kien242/MrReflow/src/Config.h

/**
 *  Copyright (C) 2018  foxis (Andrius Mikonis <andrius.mikonis@gmail.com>)
 *
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
 *  You should have received a copy of the GNU General Public License
 *  along with this program.  If not, see <http://www.gnu.org/licenses/>.
 **/

#ifndef CONFIG_H
#define CONFIG_H

#include <FS.h> //this needs to be first, or it all crashes and burns...
#include "SPIFFS.h"
#include <ArduinoJson.h>
#include <ESPAsyncWebServer.h>
#include <map>
#include "wificonfig.h"

#define RELAY 25

#define I2C_SDA 21
#define I2C_SCL 22



class Config
{
public:
  typedef struct
  {
    float P, I, D;
  } PID_t;

  class Stage
  {
  public:
    Stage(const char *n, const char *p, float t, float r, float s);

    String name;
    String pid;
    float target;
    float rate;
    float stay;
  };
  typedef std::vector<Stage>::iterator stages_iterator;

  class Profile
  {
  public:
    Profile(JsonObject &json);

    stages_iterator begin() { return stages.begin(); }
    stages_iterator end() { return stages.end(); }

    std::vector<Stage> stages;
    String name;
  };

  typedef std::map<String, Profile>::iterator profiles_iterator;

public:
  String cfgName;
  String profilesName;
  std::map<String, String> networks;

  std::map<String, PID_t> pid;
  std::map<String, Profile> profiles;

public:
  String hostname;
  String user;
  String password;
  String otaPassword;
  float measureInterval;
  float reportInterval;
  int tuner_id;
  double tuner_init_output;
  double tuner_noise_band;
  double tuner_output_step;

  typedef std::function<bool(JsonObject &json, Config *self)> THandlerFunction_parse;

public:
  Config(const String &cfg, const String &profiles);

  bool load_config();

  bool load_profiles();

  bool load_json(const String &name, size_t max_size, THandlerFunction_parse parser);

  bool save_config(AsyncWebServerRequest *request, uint8_t *data, size_t len, size_t index, size_t total);
  bool save_profiles(AsyncWebServerRequest *request, uint8_t *data, size_t len, size_t index, size_t total);

  bool save_file(AsyncWebServerRequest *request, const String &fname, uint8_t *data, size_t len, size_t index, size_t total);
};

void S_printf(const char *format, ...);

#endif
